mustafalw/far-field-measurement/SPICE designs/led_driver.asc

7420: and
D1: diode
R1: res; 56
Named nets: 0, Vin, Vout
LED
1
2
4
5
6
