mustafalw/far-field-measurement/SPICE designs/photodiode_amplifier.asc

C1: cap; 22n
C2: cap; 22µ
D1: diode; BPX65
D2: diode; 1N914
R1: res; 10k
R2: res; 1000k
R3: res; 10k
R4: res; 100k
R5: res; 69k
U1: LM308
U2: opamp
Named nets: 0, +15, -15, +5, Vout
Photodiode
2
3
4
6
7
2
3
6
